DreaM117er/Handwiring-Microboard/pic/RS.png

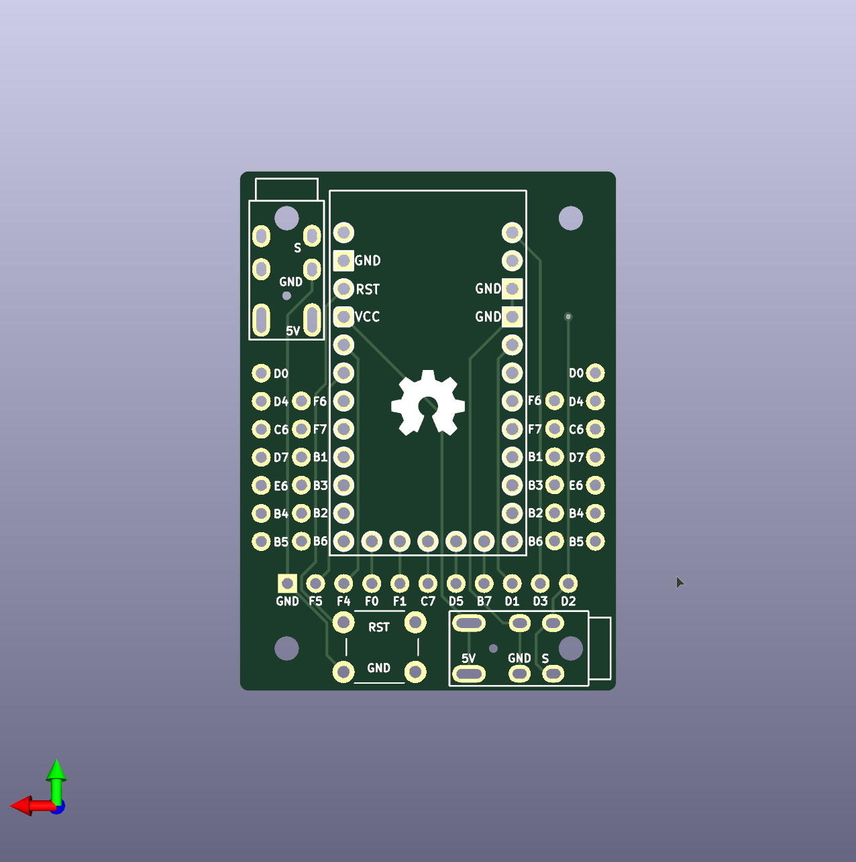
pic/RS.png
